agustinnquiroga/COMBINATION-OF-CARDIAC-AND-THERMAL-MEASUREMENTS-AS-A-PRELIMINARY-INDICATOR-OF-COCAINE-CONSUMPTION/DESIGN/IMAGENES/DSC_0426.JPG

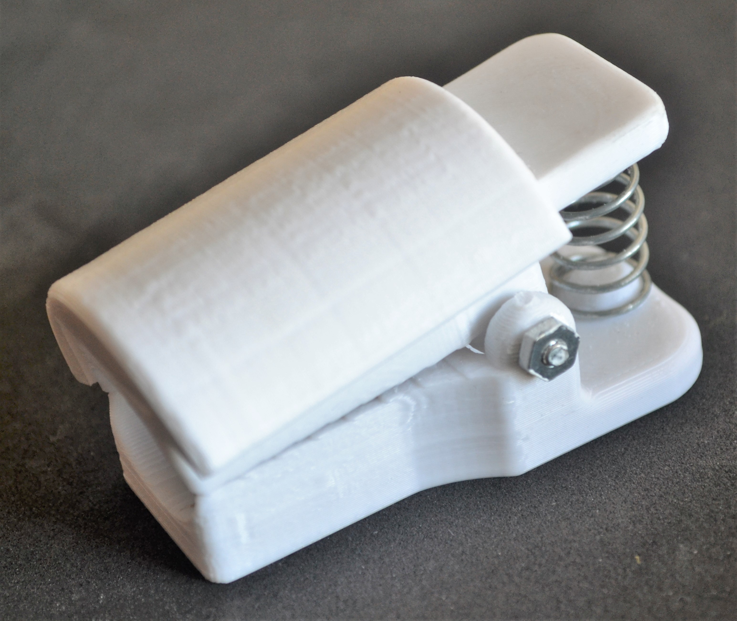
DESIGN/IMAGENES/DSC_0426.JPG
