agustinnquiroga/COMBINATION-OF-CARDIAC-AND-THERMAL-MEASUREMENTS-AS-A-PRELIMINARY-INDICATOR-OF-COCAINE-CONSUMPTION/DESIGN/IMAGENES/DSC_0427.JPG

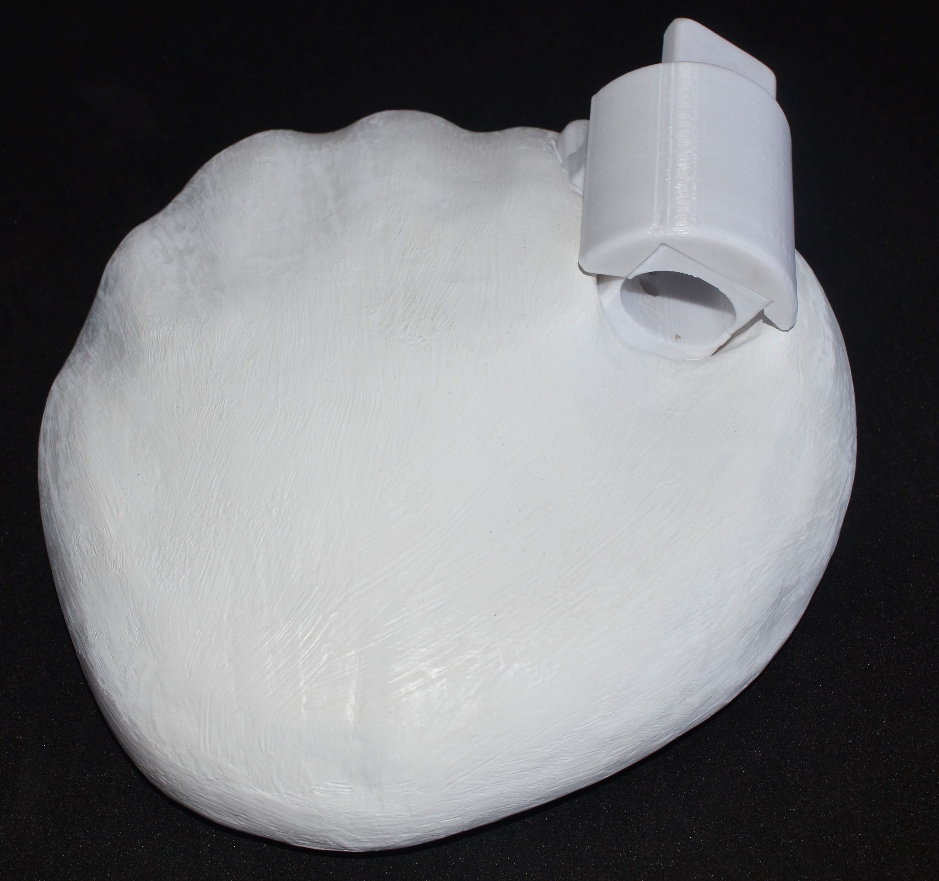
DESIGN/IMAGENES/DSC_0427.JPG
