agustinnquiroga/COMBINATION-OF-CARDIAC-AND-THERMAL-MEASUREMENTS-AS-A-PRELIMINARY-INDICATOR-OF-COCAINE-CONSUMPTION/CODE/PYTHON/ejecutable.py

# -*- coding: utf-8 -*-
"""
Editor de Spyder

Este es un archivo temporal
"""

from cx_Freeze import setup, Executable

setup(name = "ventana",
      version = "0.1",
      Description = "ventana",
      executables = [Executable("testconinterfazgrafica.py")],)
